chenyurong22/micro-affirmations/Core/Inc/messages.h

/*

File:   messages.h
Author: Isaac Pawley

*/

#ifndef INC_MESSAGES_H_
#define INC_MESSAGES_H_

#include <stddef.h>

extern const char *messages[];
extern size_t number_of_messages;

#endif /* INC_MESSAGES_H_ */
