chenyurong22/micro-affirmations/Core/Inc/matrix.h

/*

File:   matrix.h
Author: Isaac Pawley

*/

#ifndef INC_MATRIX_H_
#define INC_MATRIX_H_

#include <stdint.h>

#define PHYSICAL_ROWS 5
#define PHYSICAL_COLS 20

typedef enum {
    MATRIX_OFF = 0,
    MATRIX_ON  = 1
} MatrixBrightness_t;

void matrix_setPixel(int16_t physX, int16_t physY, MatrixBrightness_t value);
void matrix_updateMultiplex(void);

#endif /* INC_MATRIX_H_ */
